AlexDavis777/Wide-band-receiver/Schematics/Frontend.png

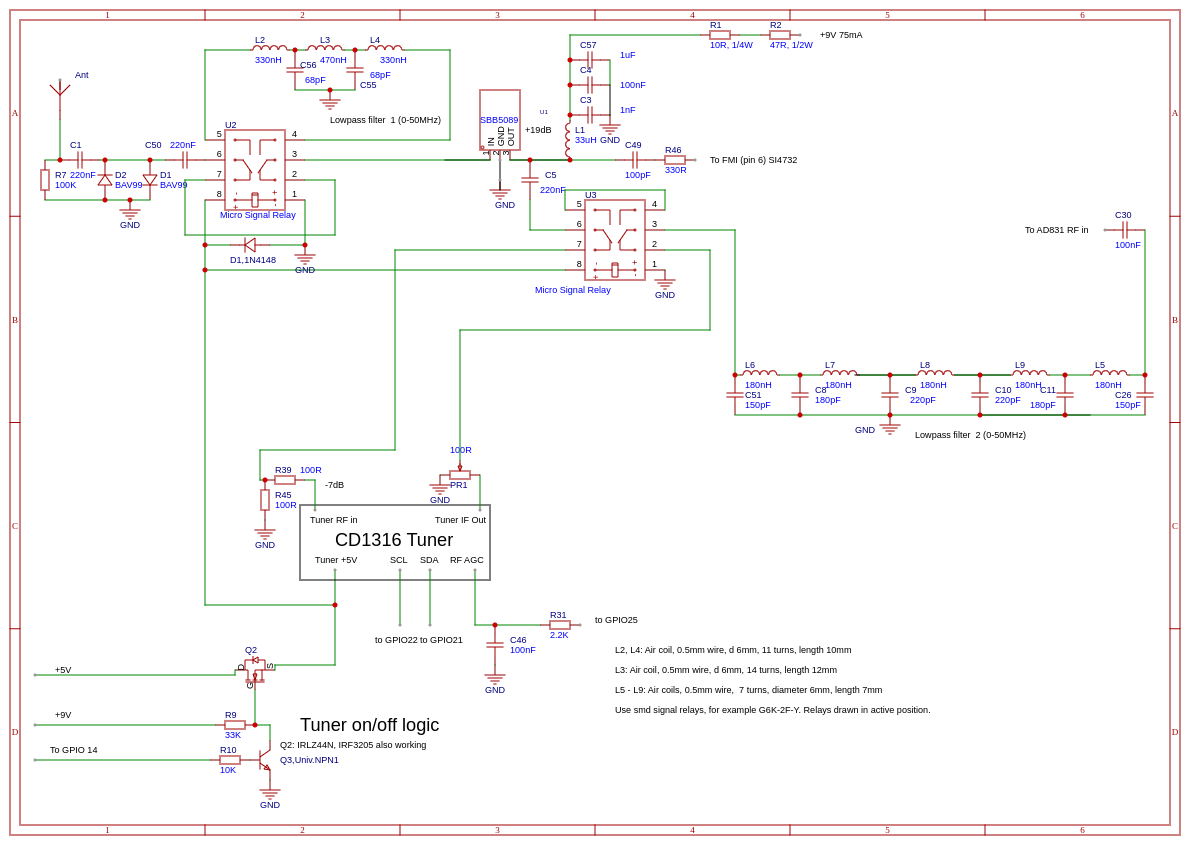
Schematics/Frontend.png
