AlexDavis777/Wide-band-receiver/Schematics/Mixer_Lo_Boost_Converter.png

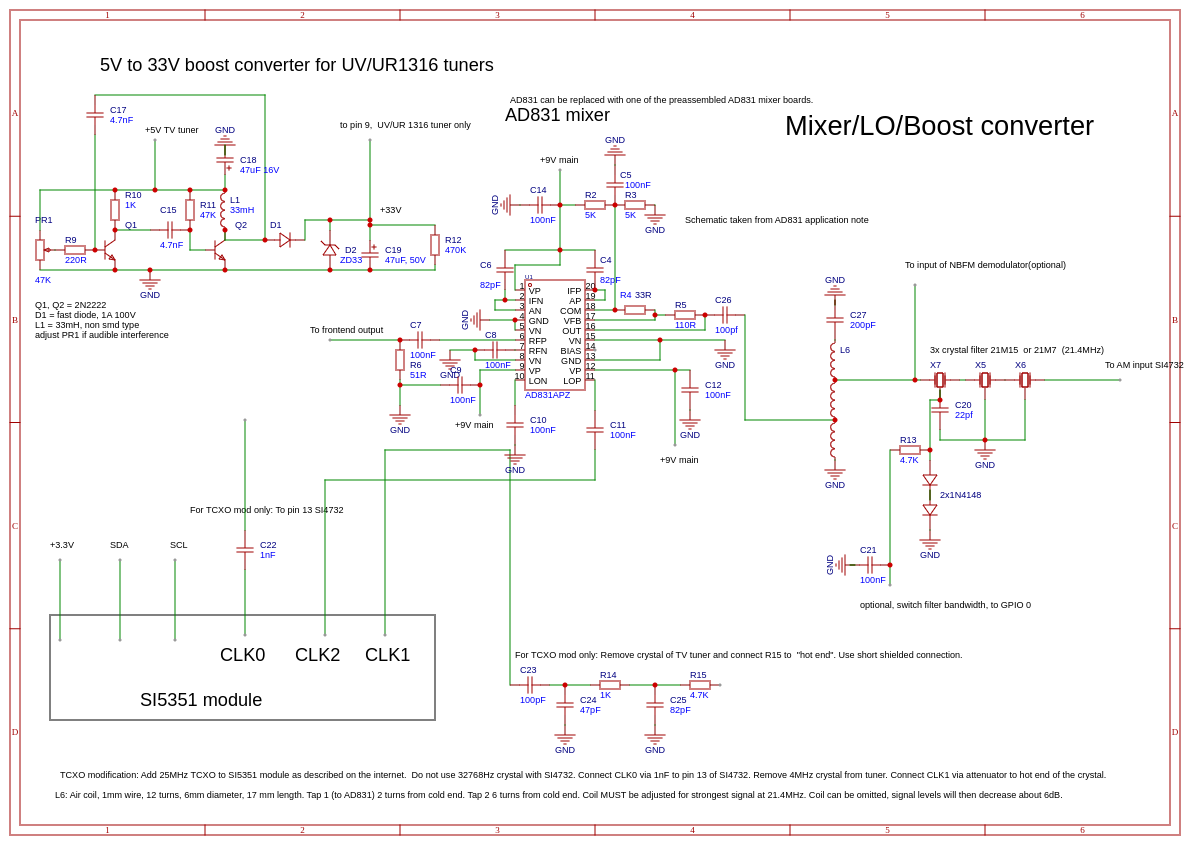
Schematics/Mixer_Lo_Boost_Converter.png
