AlexDavis777/Wide-band-receiver/Schematics/NBFM_Demodulator.png

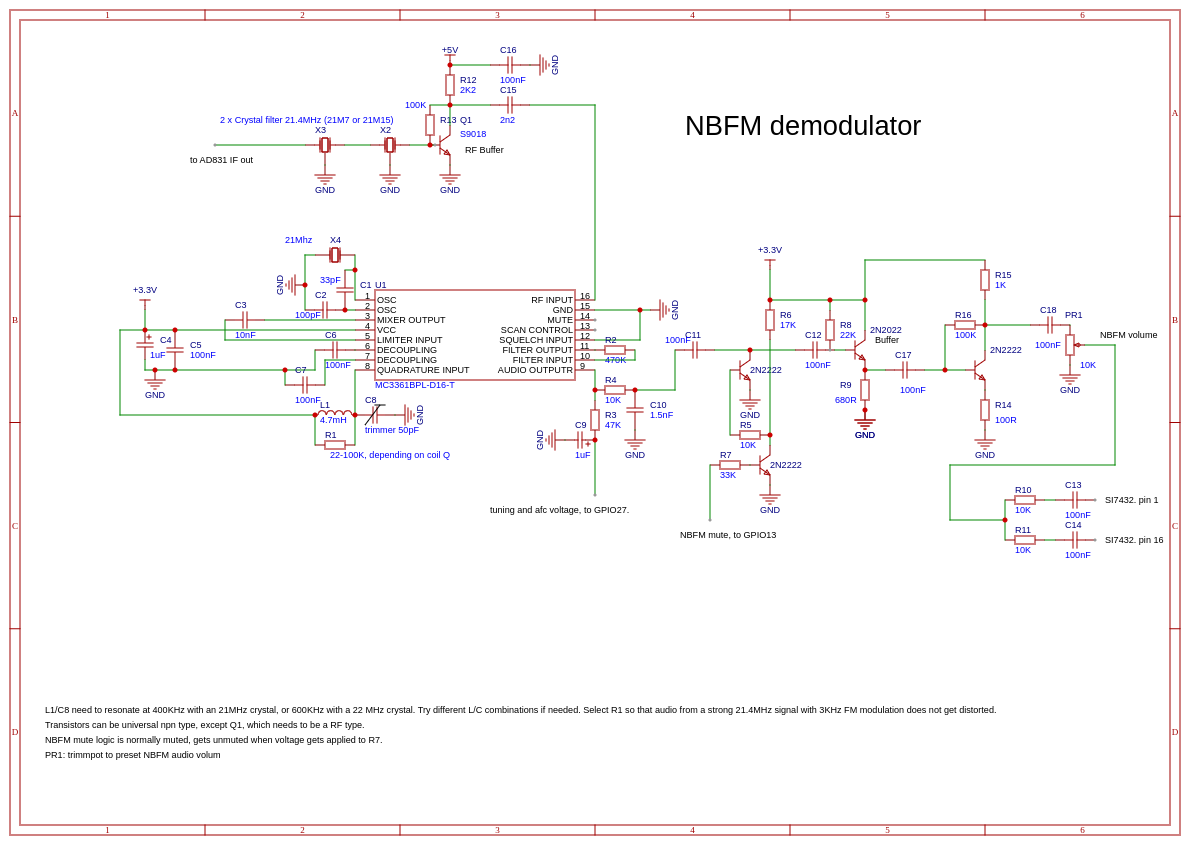
Schematics/NBFM_Demodulator.png
