AlexDavis777/Wide-band-receiver/Schematics/Optional frontend.png

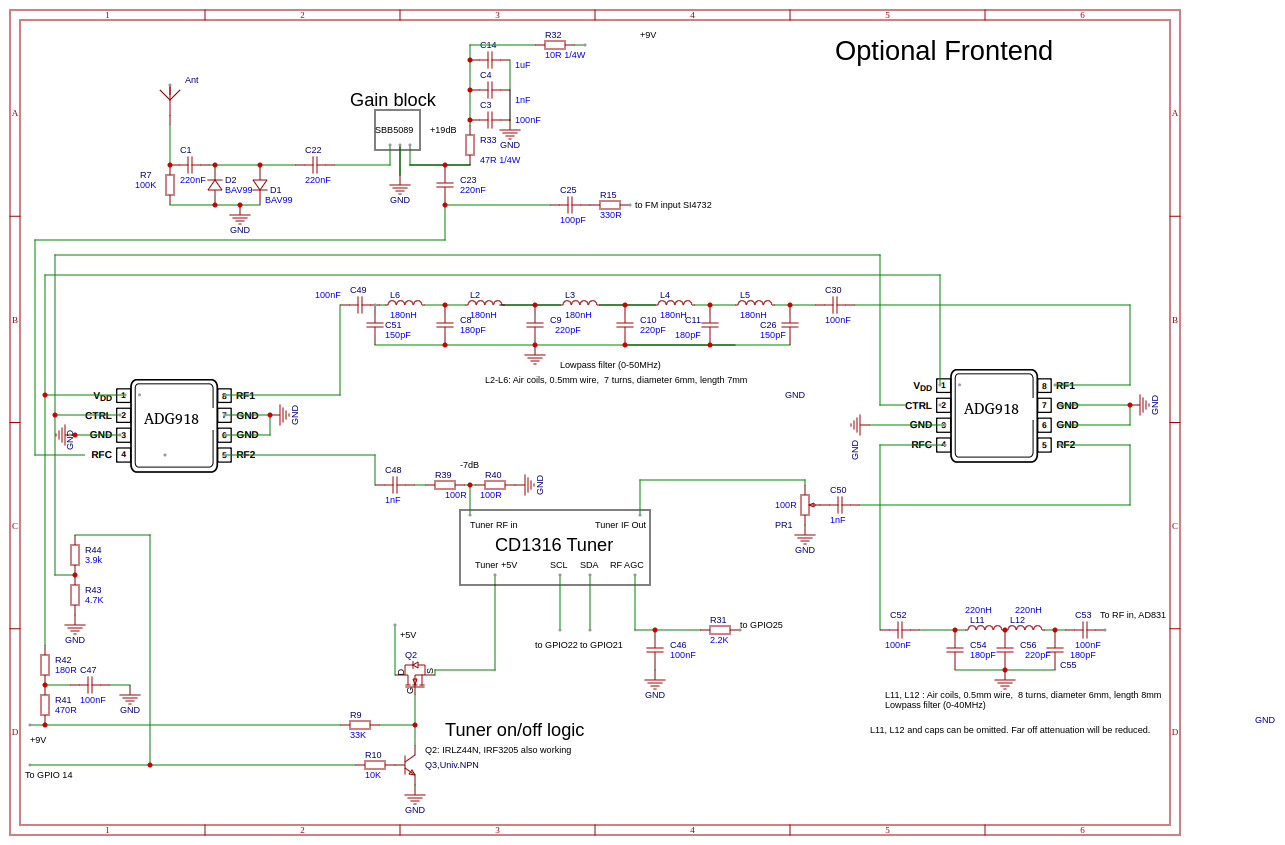
Schematics/Optional frontend.png
