AlexDavis777/Wide-band-receiver/Schematics/Processor_Demodulator_Display.png

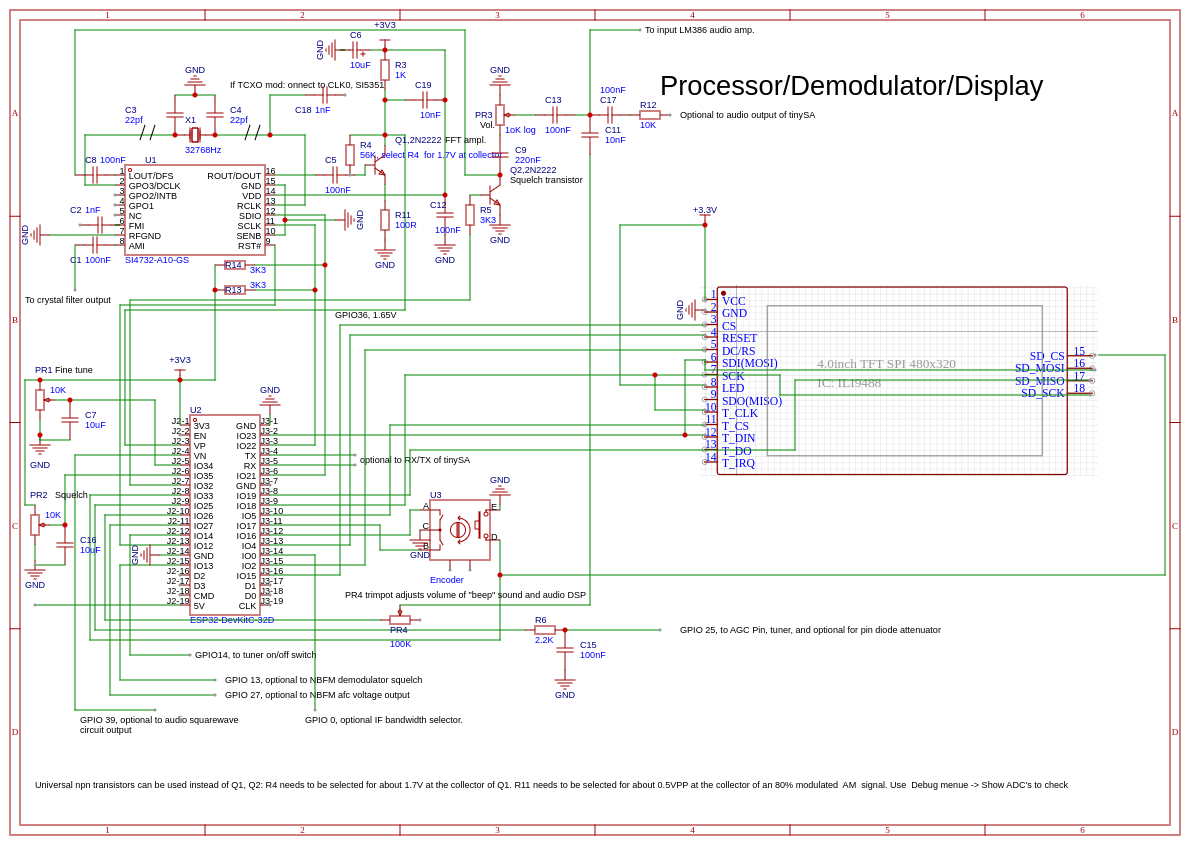
Schematics/Processor_Demodulator_Display.png
