AlexDavis777/Wide-band-receiver/ConfigScreen2.ino

void ConfigScreen2() {

  if (!altStyle)  // clear  background
    tft.fillRect(2, 61, 337, 228, TFT_BLACK);
  else
    drawButton(2, 61, 337, 228, TFT_NAVY, TFT_DARKGREY);  //Background
  draw12Buttons(TFT_BTNCTR, TFT_BTNBDR);


  redrawMainScreen = true;
  drawCf2Btns();
  readCf2Btns();
}

//##########################################################################################################################//

void drawCf2Btns() {


  struct Button {
    const int x;
    const int y;
    const char* label;
  };

  const Button buttons[] PROGMEM = {
    { 20, 132, "Touch" },
    { 20, 153, "Calibr." },
    { 100, 130, "Touch" },
    { 100, 151, "Sound" },
    { 185, 132, "Audio" },
    { 183, 151, "Waterf." },
    { 265, 132, "SetIF" },
    { 265, 151, "4732" },
    { 20, 188, "Calib" },
    { 20, 210, "SI5351" },
    { 100, 188, "Snap" },
    { 100, 210, "Freq" },
#ifndef NBFM_DEMODULATOR_PRESENT
    { 185, 190, "NBFM" },
    { 188, 210, "Shift" },
#else
    { 185, 190, "Tuning" },
    { 188, 210, "Meter" },
#endif
    { 270, 190, "FFT" },
    { 270, 210, "Gain" },
#ifdef TV_TUNER_PRESENT
    { 100, 245, "SMeter" },
    { 100, 265, "Adjust" },
#endif
    { 180, 245, "Tuner" },
    { 180, 265, "+-ppm" },
    { 267, 245, "Plain/" },
    { 267, 268, "Bitmp" }

  };

  etft.setTextColor(TFT_PINK);

  for (int i = 0; i < sizeof(buttons) / sizeof(buttons[0]); i++) {
    etft.setCursor(buttons[i].x, buttons[i].y);
    etft.print(buttons[i].label);
  }

  drawButton(8, 236, 75, 49, TFT_MIDGREEN, TFT_DARKGREEN);
  etft.setTextColor(TFT_GREEN);
  etft.setCursor(20, 245);
  etft.print(F("BACK/"));
  etft.setCursor(20, 265);
  etft.print(F("MORE"));
  etft.setTextColor(textColor);
  tDoublePress();
}
//##########################################################################################################################//

void readCf2Btns() {

  if (!pressed) return;
  int buttonID = getButtonID();

  if (!buttonID)
    return;  // outside of area

  switch (buttonID) {
    case 21:
      touchCal();
      rebuildMainScreen(1);
      break;
    case 22:
      pressSound = !pressSound;
      preferences.putBool("pressSound", pressSound);
      break;
    case 23:
      showAudioWaterfall = !preferences.getBool("audiowf", 0);
      preferences.putBool("audiowf", showAudioWaterfall);
      tft.setCursor(10, 65);
      tft.printf("Audio Waterfall: %s\n", showAudioWaterfall ? "Active" : "OFF");
      if (showAudioWaterfall) {
        tft.setCursor(10, 83);
        tft.printf("after %ds inactivity", TIME_UNTIL_ANIMATIONS);
      }
      delay(1000);
      break;
    case 24:
      setIF();
      break;
    case 31:
      calibSI5351();
      break;
    case 32:
      roundToStep = !roundToStep;
      tft.setCursor(10, 75);
      tft.printf("Round Freq to Step: %s\n", roundToStep ? "True" : "False");
      // round  FREQ up or down to the next STEP when STEP or modulation gets changed
      delay(1000);
      break;
    case 33:
#ifdef NBFM_DEMODULATOR_PRESENT
      AdjustTuningMeter();
#else
      setNBFMOffset();
#endif
      break;
    case 34:
      setFFTGain();
      break;
    case 41:
      {
        tft.setCursor(10, 80);
        tft.print(F("Short touch to return."));
        tft.setCursor(10, 100);
        tft.print(F("Long touch for more."));
        long startT = millis();
        while (get_Touch()) {  // while pressed
          if (millis() - startT > 1500) {
            ConfigScreen3();
          }
        }
      }
      break;
    case 42:
      if (!TVTunerActive)
        setSMeterCorrection(0);
      else
        setSMeterCorrection(1);
      break;
    case 43:
#ifdef TV_TUNER_PRESENT
      correctTunerOffset();
#endif
      break;
    case 44:
      altStyle = !altStyle;  // change between plain and sprite style
      preferences.putBool("lastStyle", altStyle);
      drawBigBtns();  // redraw with new style
      break;
    default:
      resetMainScreen();
      return;
  }

  redrawMainScreen = true;
  tRel();
}



//##########################################################################################################################//

void touchCal() {

  tft.fillScreen(TFT_BLACK);               // Clear the screen
  tft.setTextColor(TFT_WHITE, TFT_BLACK);  // Set text color to white with black background
  tft.setTextSize(2);

  uint16_t calData[5];

  tft.fillScreen(TFT_BLACK);
  tft.setCursor(20, 0);

  tft.setTextSize(1);
  tft.setTextColor(TFT_WHITE, TFT_BLACK);

  tft.println(F("Touch corners as indicated"));

  tft.println();

  tft.calibrateTouch(calData, TFT_WHITE, TFT_RED, 15);

  tft.setTextSize(2);
  tft.setCursor(0, 30);
  tft.print(F("Calibration complete!\nTouch screen with stylus\nto test different areas.\nDot must appear close to stylus\nPRESS encoder to save\nOr MOVE encoder to recalibrate\n"));
  tft.printf("Cal Data: %d, %d, %d, %d, %d\n", calData[0], calData[1], calData[2], calData[3], calData[4]);


  while (true) {
    if ((digitalRead(ENCODER_BUTTON) == LOW))
      break;

    if (clw || cclw) {
      clw = false;
      cclw = false;
      tft.fillScreen(TFT_BLACK);
      tft.setCursor(0, 20);
      tft.print(F("Recalibration\nTouch screen with stylus\nto test different areas\n\n"));
      tft.calibrateTouch(calData, TFT_WHITE, TFT_RED, 15);
      tft.printf("Cal Data: %d, %d, %d, %d, %d\n", calData[0], calData[1], calData[2], calData[3], calData[4]);
    }

    get_Touch();
    if (pressed)
      tft.fillCircle(tx, ty, 3, TFT_YELLOW);
    pressed = false;
    delay(10);
    tft.fillCircle(tx, ty, 3, TFT_BLACK);
  }

  //write to flash
  preferences.putInt("cal0", calData[0]);
  preferences.putInt("cal1", calData[1]);
  preferences.putInt("cal2", calData[2]);
  preferences.putInt("cal3", calData[3]);
  preferences.putInt("cal4", calData[4]);

  // Apply calibration data
  tft.setTouch(calData);

  tft.print(F("Calibration data saved."));

  delay(1000);
}

//##########################################################################################################################//

void setNBFMOffset() {  // set best offset from crystal filter center frequency for flank demodulation

  int offset = 0, oldOffset = 0;
  encLockedtoSynth = false;

  tft.fillRect(5, 65, 333, 225, TFT_BLACK);

  tft.setCursor(5, 65);
  tft.print(F("Use encoder to set NBFM"));


  tft.setCursor(5, 82);
  tft.print(F("shift for flank demodulation"));

  tft.setCursor(5, 100);
  tft.print(F("Set for least distortion"));

  tft.setCursor(5, 120);
  tft.print(F("Press encoder to save"));

  offset = preferences.getInt("NBFMOffset", 0);
  tft.fillRect(5, 140, 320, 17, TFT_BLACK);
  tft.setCursor(5, 140);
  tft.printf("NBFM Offset: %d", offset);


  while (digitalRead(ENCODER_BUTTON) == HIGH) {

    if (oldOffset != offset) {
      tft.fillRect(5, 140, 320, 17, TFT_BLACK);
      tft.setCursor(5, 140);
      tft.printf("NBFM Offset: %d KHz", offset);
      si4735.setAM(520, 29900, SI4735TUNED_FREQ + offset, 1);
      oldOffset = offset;
    }

    delay(50);
    if (clw) {
      offset++;
    }

    if (cclw) {
      offset--;
    }

    clw = false;
    cclw = false;
  }

  while (digitalRead(ENCODER_BUTTON) == LOW)
    ;

  preferences.putInt("NBFMOffset", offset);

  loadSi4735parameters();

  encLockedtoSynth = true;
  clearStatusBar();
}

//##########################################################################################################################//

#ifdef TV_TUNER_PRESENT

void correctTunerOffset() {  //corrects tuner frequency error.

  tunerOffsetPPM = preferences.getInt("tunerOffsetPPM", 0);
  encLockedtoSynth = false;

  tft.fillRect(5, 63, 333, 229, TFT_BLACK);
  calculateAndDisplaySignalStrength();

  tft.setCursor(5, 90);
  tft.print(F("Use encoder to compensate"));

  tft.setCursor(5, 107);
  tft.print(F("for tuner freq error."));

  tft.setCursor(5, 130);
  tft.print(F("Press encoder to save."));
  tft.fillRect(5, 170, 320, 17, TFT_BLACK);
  tft.setCursor(5, 170);
  tft.printf("Correction: %dppm", tunerOffsetPPM);

  while (digitalRead(ENCODER_BUTTON) == HIGH) {

    if (clw || cclw) {

      calculateAndDisplaySignalStrength();
      tft.fillRect(5, 170, 320, 17, TFT_BLACK);
      tft.setCursor(5, 170);
      tft.printf("Correction: %dppm", tunerOffsetPPM);
      clw = false;
      cclw = false;
    }

    delay(50);


    if (clw) {
      tunerOffsetPPM++;
    }

    if (cclw) {
      tunerOffsetPPM--;
    }


    OLDPLLFREQ = PLLFREQ - 1;  // needed to generate the I2C bus packet
    programTVTuner();          // send a new telegram
  }

  while (digitalRead(ENCODER_BUTTON) == LOW)
    ;

  preferences.putInt("tunerOffsetPPM", tunerOffsetPPM);
  OLDPLLFREQ = PLLFREQ - 1;
  programTVTuner();
  encLockedtoSynth = true;
  clearStatusBar();
}


#endif

//##########################################################################################################################//

void setSMeterCorrection(bool mode) {  // adjusts gain for : 0 = SW S Meter, 1 = VHF/UHF S Meter

  int8_t GainCorrection;

  encLockedtoSynth = false;
  clearStatusBar();
  clearNotification();
  DrawSmeterScale();

  tft.setCursor(10, 90);
  tft.setTextColor(TFT_WHITE);

  if (!mode) {
    GainCorrection = SWGainCorrection;  // load last calibration factor
    tft.print(F("For shortwave only."));
  }

  else {
    GainCorrection = tunerGainCorrection;  // load last calibration factor
    tft.print(F("For VHF/UHF only."));
  }


  tft.setCursor(10, 105);
  tft.printf("Gain corr.:%d dB", GainCorrection);

  while (digitalRead(ENCODER_BUTTON) == HIGH) {

    if (clw)
      GainCorrection++;
    if (cclw)
      GainCorrection--;



    if (clw || cclw) {

      if (mode)
        tunerGainCorrection = GainCorrection;
      else
        SWGainCorrection = GainCorrection;

      tft.fillRect(10, 105, 325, 16, TFT_BLACK);
      tft.setCursor(10, 105);
      tft.printf("Gain corr.:%d dB", GainCorrection);

      clw = false;
      cclw = false;
    }

    getRSSIAndSNR();
    delay(30);
    calculateAndDisplaySignalStrength();
    displaySmeterBar(4);
  }

  if (!mode)
    preferences.putChar("swgc", SWGainCorrection);
  else {
    preferences.putChar("tgc", tunerGainCorrection);
  }
  encLockedtoSynth = true;
  tft.setTextColor(textColor);
  while (digitalRead(ENCODER_BUTTON) == LOW)
    ;
}

//##########################################################################################################################//

void setFFTGain() {  // sets gain (amplitude) for the AF spectrum analyzers and the minioscilloscope

  FFTGain = preferences.getInt("FFTGain", 100);  // load last calibration factor

 static uint8_t oldFFTGain = 0; 
  encLockedtoSynth = false;
  clearStatusBar();
 char save = miniWindowMode;

  miniWindowMode = 3; // mini oscilloscope 
  while (digitalRead(ENCODER_BUTTON) == HIGH) {
    clearNotification();

    if (clw)
      FFTGain += 5;
    if (cclw)
      FFTGain -= 5;
    clw = false;
    cclw = false;

    FFTGain = constrain(FFTGain, 1, 255);
     
    if(FFTGain != oldFFTGain) { 
    tft.fillRect(5, 100, 333, 16, TFT_BLACK);
    tft.setCursor(5, 100);
    tft.printf("FFT Gain :%d ", FFTGain);
    oldFFTGain = FFTGain;
    }
   
  
    audioSpectrum(); // miniwindow
  
  }

  preferences.putInt("FFTGain", FFTGain);
  while (digitalRead(ENCODER_BUTTON) == LOW)
    ;
  encLockedtoSynth = true;
   miniWindowMode = save; 
}


//##########################################################################################################################//
#ifdef NBFM_DEMODULATOR_PRESENT

void AdjustTuningMeter() {

  encLockedtoSynth = false;

  tft.setCursor(5, 64);
  tft.print("Set tuning meter sensitivity");
  tft.setCursor(5, 80);
  tft.print("Press encoder when done");

  clw = true;
  cclw = true;

  while (digitalRead(ENCODER_BUTTON) == HIGH) {

    if (clw)
      tuningMeterDivider--;
    if (cclw)
      tuningMeterDivider++;



    if (clw || cclw) {

      tuningMeterDivider = constrain(tuningMeterDivider, 1, 25);
      tft.fillRect(5, 100, 330, 16, TFT_BLACK);
      tft.setCursor(5, 100);
      tft.printf("Sensitivity: %d", 26 - tuningMeterDivider);

      clw = false;
      cclw = false;
    }
  }


  preferences.putUChar("tmd", tuningMeterDivider);



  tft.fillRect(5, 64, 333, 60, TFT_BLACK);
  displayText(10, 64, 0, 0, "Auto adjusting ");
  tft.setTextSize(2);
  displayText(10, 84, 0, 0, "tuning meter...");

  do {
    getDiscriminatorVoltage();
      delay(5);

    if (afcVoltage > 0)
      discriminatorZero++;
    if (afcVoltage < 0)
      discriminatorZero--;

    tft.fillRect(50, 105, 80, 20, TFT_BLACK);
    tft.setCursor(10, 105);
    tft.printf("Offs: %d", afcVoltage);
  }

  while (afcVoltage);

  tft.fillRect(10, 105, 125, 20, TFT_BLACK);
  tft.setCursor(10, 105);
  tft.printf("READY!");

  preferences.putInt("dZero", discriminatorZero);
  encLockedtoSynth = true;

  delay(1000);
}
#endif
//##########################################################################################################################//
