AlexDavis777/Wide-band-receiver/WAVRecorder.ino

// wav recorder and player. Depends heavily on the quality of the SD card. Uses <SdFat.h> library for faster writing

// Settings
#define SAMPLE_RATE 8000  // 4KHz
#define SAMPLE_INTERVAL (1000000 / SAMPLE_RATE)
#define RECORD_TIME 9999
#define BUFFER_SIZE frSize

// WAV file header structure
typedef struct {
  char chunkID[4];         // "RIFF"
  uint32_t chunkSize;      // File size - 8
  char format[4];          // "WAVE"
  char subchunk1ID[4];     // "fmt "
  uint32_t subchunk1Size;  // 16 for PCM
  uint16_t audioFormat;    // 1 = PCM
  uint16_t numChannels;    // 1 = mono
  uint32_t sampleRate;
  uint32_t byteRate;       // sampleRate * numChannels * bitsPerSample/8
  uint16_t blockAlign;     // numChannels * bitsPerSample/8
  uint16_t bitsPerSample;  // 8
  char subchunk2ID[4];     // "data"
  uint32_t subchunk2Size;  // data size
} WavHeader_8bit;


//##########################################################################################################################//

//Forward decl
void createWavHeader8bit(WavHeader_8bit* header, uint32_t sampleCount);

//##########################################################################################################################//


void mountSDCard() {
  tft.endWrite();
  digitalWrite(TFT_CS, HIGH);
  digitalWrite(TFT_CS, LOW);  // GPIO33 for SD CS
  uint16_t ctr = 0;

  while (!sd.begin(SD_CS, SD_SCK_MHZ(25))) {  // <SdFat.h>
    ctr++;
    displayText(300, 300, 179, 15, "Mounting SDcard");

    if (ctr == 10) {
      Serial_print(" Mount failed!\n");
      displayText(300, 300, 179, 16, "Mount failed");
      return;
    }
    delay(100);
  }

  displayText(300, 300, 179, 16, "SD card mounted");
  delay(500);
  displayText(300, 300, 179, 16, " ");
}

//##########################################################################################################################//
void wavRecord(uint8_t mode) {  // 0 = plain, 1 = timer, 2 = squelch

  if (mode == 1) {
    bool result = getStartEndTime();
    if (!result)
      return;
  }

  int endHour = recordEndTime / 100;  // 17
  int endMin = recordEndTime % 100;   // 59




  tft.setTextColor(TFT_YELLOW);
  tft.fillRect(5, 65, 333, 225, TFT_BLACK);


  if (mode == 2) {
    tft.setCursor(8, 70);
    tft.print(F("Records only when"));
    tft.setCursor(8, 90);
    tft.print(F("squelch is open."));

    tft.setCursor(8, 170);
    tft.print(F("While recording, only the "));
    tft.setCursor(8, 190);
    tft.print(F("squelch can be adjusted."));
  }


  tft.setCursor(8, 130);
  tft.print(F("Move encoder to stop rec."));
  tft.setCursor(8, 220);
  tft.print(F("Creates consecutive .wav"));
  tft.setCursor(8, 240);
  tft.print(F("files on SDCard."));
  tft.setCursor(8, 260);
  tft.print(F("8 Bit Mono, 8000 sampl/sec"));

  bool circle = false;
  bool mutestat = audioMuted;

  si4735.setHardwareAudioMute(false);
  mountSDCard();

  // Find next avail file name
  int fileIndex = 1;
  String fileName;
  do {
    fileName = "/rec" + String(fileIndex) + ".wav";
    fileIndex++;
  } while (sd.exists(fileName.c_str()));  // use sd.exists() with SdFat

  f = sd.open(fileName.c_str(), O_WRITE | O_CREAT | O_TRUNC);
  if (!f) {
    Serial_println("Faild to create file!");
    displayText(300, 300, 179, 15, "Failed to create file");
    return;
  }

  displayText(220, 300, 259, 15, "Recording:");
  tft.print(fileName);

  // Build WAV header
  WavHeader_8bit header;
  createWavHeader8bit(&header, RECORD_TIME * SAMPLE_RATE);
  f.write((uint8_t*)&header, sizeof(header));
  
  uint16_t ctr = 0;
  audioBufSize = frSize; // 4096 need full size 
  recordWav = true;
  bufferPlaying = false;
  playIndex = 0;


  while (!(clw + cclw)) {  //encoder moved


    if (mode == 2) {

      ctr++;

      if (ctr == 2) {  // indroduces delay before the squelch closes
        ctr = 0;
        si4735.getCurrentReceivedSignalQuality(0);
        signalStrength = si4735.getCurrentRSSI();
        readSquelchPot(0);
        if (signalStrength > currentSquelch)
          si4735.setAudioMute(false);
        else
          si4735.setAudioMute(true);
      }
    }




    if ((signalStrength > currentSquelch) || mode < 2)

    {

      if (!circle) {
        tft.fillCircle(5, 310, 5, TFT_RED);
        circle = true;
      }



      if (bufferFilled) { // buffer gets filled by timer interrupt 125uS
          f.write((uint8_t*)frame, BUFFER_SIZE);
          bufferFilled = false;
      }


      if (mode == 1) {  // timer mode
        getLocalTime(&timeinfo);
        if (timeinfo.tm_hour == endHour && timeinfo.tm_min == endMin)
          break;
      }
    }

    else {
      tft.fillCircle(5, 310, 5, TFT_BLACK);
      circle = false;
    }
  }


  clw = false;
  cclw = false;
  recordWav = false;
 

  f.flush();
  f.close();
  mutestat = audioMuted;
  si4735.setAudioMute(mutestat);
  si4735.setHardwareAudioMute(mutestat);
  displayText(280, 300, 199, 15, "Finished");
  delay(500);
  tft.fillRect(220, 300, 259, 19, TFT_BLACK);
  tft.setTextColor(textColor);
  digitalWrite(TFT_CS, LOW);
  digitalWrite(SD_CS, INPUT_PULLUP);
  return;
}


//##########################################################################################################################//
void createWavHeader8bit(WavHeader_8bit* header, uint32_t sampleCount) {
  // RIFF chunk
  memcpy(header->chunkID, "RIFF", 4);
  header->chunkSize = sampleCount + 36;  // 8-bit samples
  memcpy(header->format, "WAVE", 4);

  // Format subchunk
  memcpy(header->subchunk1ID, "fmt ", 4);
  header->subchunk1Size = 16;
  header->audioFormat = 1;  // PCM
  header->numChannels = 1;  // Mono
  header->sampleRate = SAMPLE_RATE;
  header->byteRate = SAMPLE_RATE;  // sampleRate × channels × (8/8)
  header->blockAlign = 1;          // channels × (8/8)
  header->bitsPerSample = 8;

  // Data subchunk
  memcpy(header->subchunk2ID, "data", 4);
  header->subchunk2Size = sampleCount;  // samples × channels × (8/8)
}
//##########################################################################################################################//


// basic .wav player

void playWavFile() {

  String selected = selectFileWithExtension(".wav");

  FsFile f = sd.open(selected.c_str(), O_READ);
  if (!f) {
    tft.print(F("Failed to open."));
    tft.println(selected);
    delay(1000);
    rebuildMainScreen(false);
    redrawIndicators();
    return;
  }

  WavHeader_8bit header;
  f.read((uint8_t*)&header, sizeof(header));

  if (header.audioFormat != 1 || header.numChannels != 1 || header.bitsPerSample != 8) {
    Serial.println("Unsupported WAV format");
    f.close();
    return;
  }

  si4735.setAudioMute(true);

  int bytesAvailable = 9999;
  bool read = false;

  while (bytesAvailable > 0) {

  if (!read) {  
    bufferPlaying = true; // play via ISR
    bytesAvailable = f.read( playBuffer, 512); // load into the ISR play buffer
    read = true;
  } 

  while (bufferPlaying);
   read = false;

    if (clw || cclw)
      break;
  }

  f.close();
  clw = false;
  cclw = false;
  si4735.setAudioMute(false);
  rebuildMainScreen(false);
  bufferPlaying = false;
  playIndex = 0;
}


//##########################################################################################################################//


String selectFileWithExtension(const char* extension) {
  mountSDCard();

  FsFile dir = sd.open("/");
  if (!dir) {
    Serial.println("Failed to open root directory!");
    redrawIndicators();
    return "";
  }

  const int MAX_FILES = 24;  // more corrupts the stack
  const int NAME_LEN = 64;

  char files[MAX_FILES][NAME_LEN];
  int fileCount = 0;

  FsFile file;

  while (file.openNext(&dir, O_RDONLY)) {
    if (!file.isDir() && fileCount < MAX_FILES) {

      char name[NAME_LEN];
      file.getName(name, sizeof(name));

      String fname = name;
      String ext = extension;
      fname.toLowerCase();
      ext.toLowerCase();

      if (fname.endsWith(ext)) {
        strncpy(files[fileCount], name, NAME_LEN);
        files[fileCount][NAME_LEN - 1] = 0;
        fileCount++;
      }
    }
    file.close();
  }

  dir.close();

  if (fileCount == 0) {
    tft.fillScreen(TFT_BLACK);
    tft.setTextColor(TFT_RED);
    tft.setCursor(10, 150);
    tft.printf("No %s files found!", extension);
    return "";
  }

  int selected = 0;
  int indx = 0;

  const int maxRows = 12;  // 12 rows per screen
  bool redraw = true;

  tft.fillScreen(TFT_BLACK);
  tft.setTextColor(TFT_WHITE);
  tft.setCursor(10, 0);
  tft.printf("Select %s file and press encoder.", extension);
  tft.setCursor(25, 300);
  tft.print(F("Move encoder to stop playing."));


  while (true) {  // file name drawing routine

    if (redraw || clw || cclw) {

      for (int i = 0; i < maxRows; i++) {

        int y = 30 + i * 22;

        tft.fillRect(0, y, 480, 22, TFT_BLACK);

        if ((indx + i) < fileCount) {

          if ((indx + i) == selected)
            tft.setTextColor(TFT_YELLOW);
          else
            tft.setTextColor(TFT_GREY);

          tft.setCursor(10, y);
          tft.print(files[indx + i]);
        }
      }

      redraw = false;
    }

    if (cclw) {
      if (selected > 0) {
        selected--;
        if (selected < indx) indx--;
      }
      cclw = false;
      redraw = true;
    }

    if (clw) {
      if (selected < fileCount - 1) {
        selected++;
        if (selected >= indx + maxRows) indx++;
      }
      clw = false;
      redraw = true;
    }

    if (digitalRead(ENCODER_BUTTON) == LOW) {

      delay(30);
      while (digitalRead(ENCODER_BUTTON) == LOW)
        ;

      return String(files[selected]);
    }

    delay(5);
  }
}
//##########################################################################################################################//

bool getStartEndTime() {  // for timer record


  tft.fillScreen(TFT_BLACK);

  if (!timeSet) {
    tft.setCursor(10, 10);
    tft.print("Time not set.");
    tft.setCursor(10, 30);
    tft.print("Starting WIFI to set time...");
    tft.setCursor(10, 50);
    tft.print("Time format is UTC.");
    getTime();
  }

  else
    getLocalTime(&timeinfo);
  tft.setCursor(120, 300);
  tft.print(&timeinfo, "Time %H%M UTC");

  drawNumPad();
  drawKeypadButtons();
  tft.fillRect(4, 4, 470, 45, TFT_BLACK);
  tft.setCursor(10, 20);
  tft.print(F("Enter start time (HHMM) and RETURN."));
  tPress();
  readKeypadButtons(false);

  recordStartTime = keyVal;

  drawNumPad();
  drawKeypadButtons();
  tft.fillRect(4, 4, 470, 45, TFT_BLACK);
  tft.setCursor(10, 20);
  tft.print(F("Enter end time (HHMM) and RETURN."));
  tPress();  // wait until pressed
  readKeypadButtons(false);

  recordEndTime = keyVal;

  tft.setCursor(10, 30);
  tft.printf("Record programmed for %d to %d UTC.", recordStartTime, recordEndTime);


  int startHour = recordStartTime / 100;  // 17
  int startMin = recordStartTime % 100;   // 59
  tft.setCursor(10, 300);
  tft.print("Time now:");

  while (true) {
    getLocalTime(&timeinfo);

    tft.fillRect(120, 300, 300, 20, TFT_BLACK);
    tft.setCursor(120, 300);
    tft.print(&timeinfo, "%H%M UTC");
    delay(1000);

    if (timeinfo.tm_hour == startHour && timeinfo.tm_min == startMin) {
      tft.fillRect(10, 25, 470, 295, TFT_BLACK);
      return true;
    } else if (clw + cclw) {
      clw = false;
      cclw = false;
      return false;
    }
  }
}
